sathyanc/Tinker-Slider-v1.0/Schematic/Tinker Slider v1.0.sch

## EAGLE design Schematic/Tinker Slider v1.0.sch (2018-11-24)

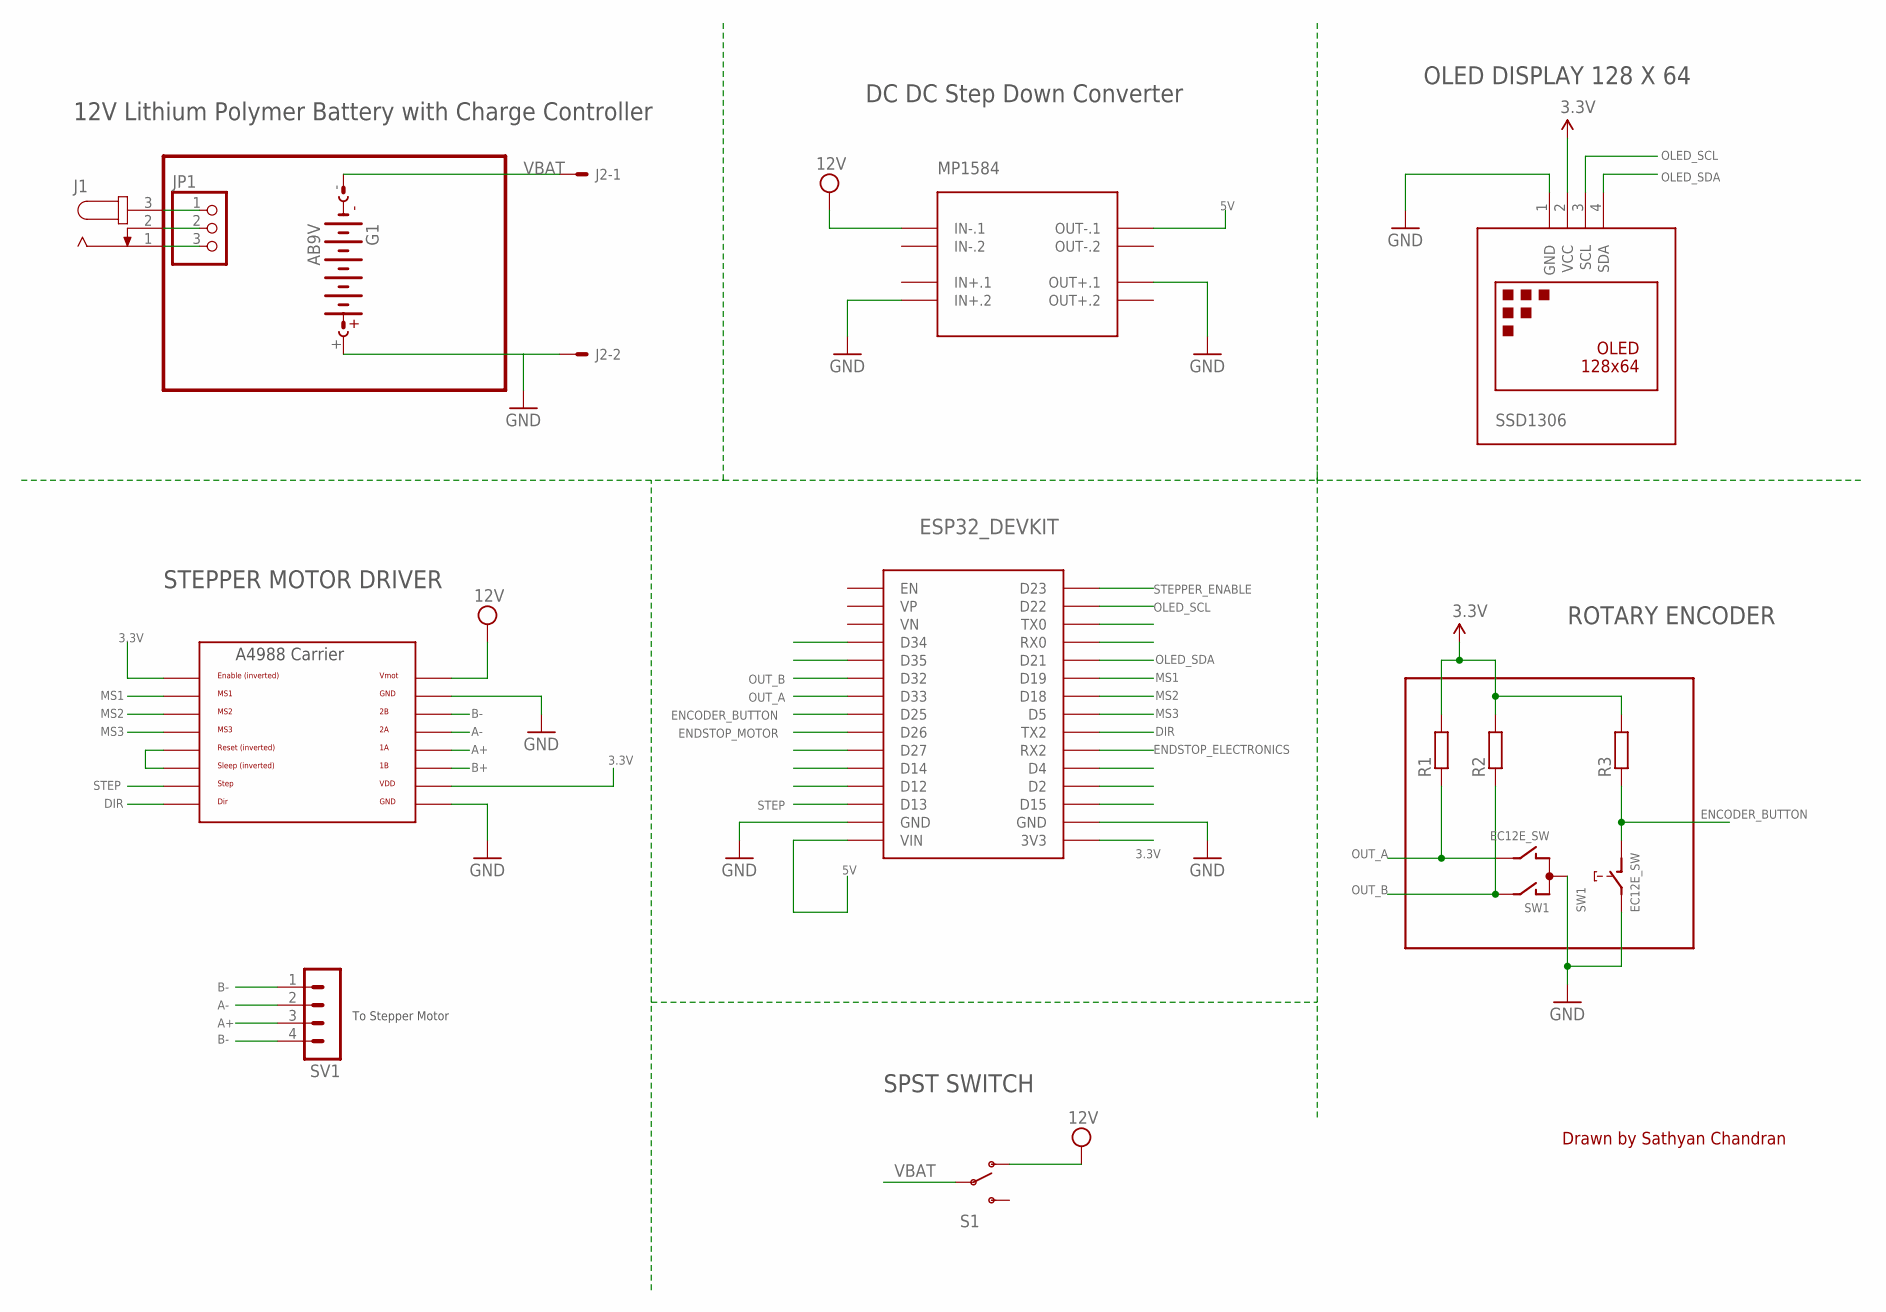
[picture p16: schematic Tinker Slider v1.0.sch]

Parts:
G1: AB9V
J1: JACK-PLUG0; SPC4077
J2: 22-27-2021-02; 6410-02
JP1: PINHD-1X3; 1X03
MP1584: DC-DC-STEP-DOWN-MP1584
R1, R2, R3: R-EU_R0805; R0805
S1: SWITCH-SPSTKIT; SWITCH-SPDT_KIT
SSD1306: DISPLAY-OLED-128X64-I2C
SV1: MA04-1
SW1: EC12E_SW; ALPS_EC12E_SW
U$3: ESP32_DEVKIT
U$5: A4983CARRIER; A4988BREAKOUT

Connections:
3.3V: U$3.3V3, U$5.EN, U$5.VDD
5V: MP1584.OUT-.1, U$3.VIN
A+: SV1.3, U$5.1A
A-: SV1.2, U$5.2A
B+: U$5.1B
B-: SV1.1, SV1.4, U$5.2B
DIR: U$3.TX2, U$5.DIR
ENCODER_BUTTON: R3.1, SW1.D (1), U$3.D25
ENDSTOP_ELECTRONICS: U$3.RX2
ENDSTOP_MOTOR: U$3.D26
GND: G1.+, J2.2, MP1584.IN+.2, MP1584.OUT+.1, SSD1306.1 (GND), SW1.C, SW1.E (2), U$3.GND@1 (GND), U$3.GND@2 (GND), U$5.GND, U$5.GND@0 (GND)
MS1: U$3.D19, U$5.MS1
MS2: U$3.D18, U$5.MS2
MS3: U$3.D5, U$5.MS3
unnamed: U$5.RST, U$5.SLP (SLEEP)
unnamed: J1.3, JP1.1
unnamed: J1.2, JP1.2
unnamed: J1.1, JP1.3
OLED_SCL: SSD1306.3 (SCL), U$3.D22
OLED_SDA: SSD1306.4 (SDA), U$3.D21
OUT_A: R1.1, SW1.B, U$3.D33
OUT_B: R2.1, SW1.A, U$3.D32
STEP: U$3.D13, U$5.STEP
STEPPER_ENABLE: U$3.D23
VBAT: G1.-, J2.1, S1.2
VCC: MP1584.IN-.1, R1.2, R2.2, R3.2, S1.1 (O), SSD1306.2 (VCC), U$5.VMOT

Notes on the sheet:
12V Lithium Polymer Battery with Charge Controller
OLED DISPLAY 128 X 64
ROTARY ENCODER
STEPPER MOTOR DRIVER
SPST SWITCH
DC DC Step Down Converter
To Stepper Motor
Drawn by Sathyan Chandran
